Teslafly/Moxie_drive_mini_drv/3dmodels/xt-60-family-1.snapshot.6/xt60 fam1.PNG

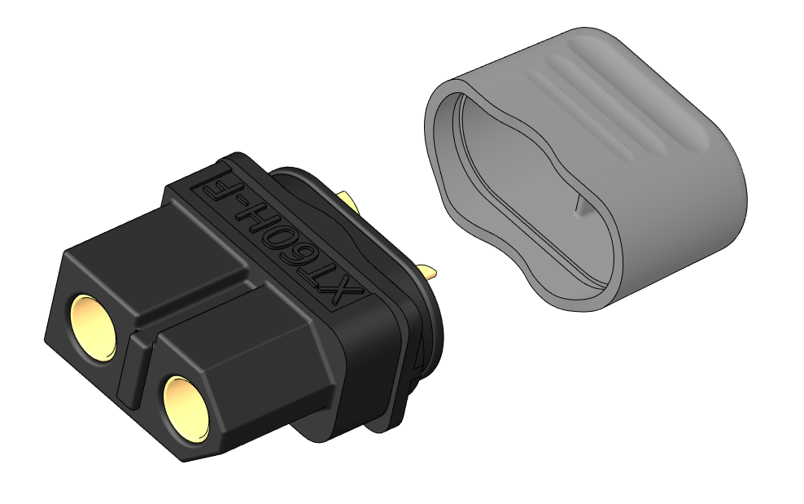
3dmodels/xt-60-family-1.snapshot.6/xt60 fam1.PNG
