Teslafly/Moxie_drive_mini_drv/3dmodels/MachineScrews/Screw_Machine_M3x14.SLDPRT

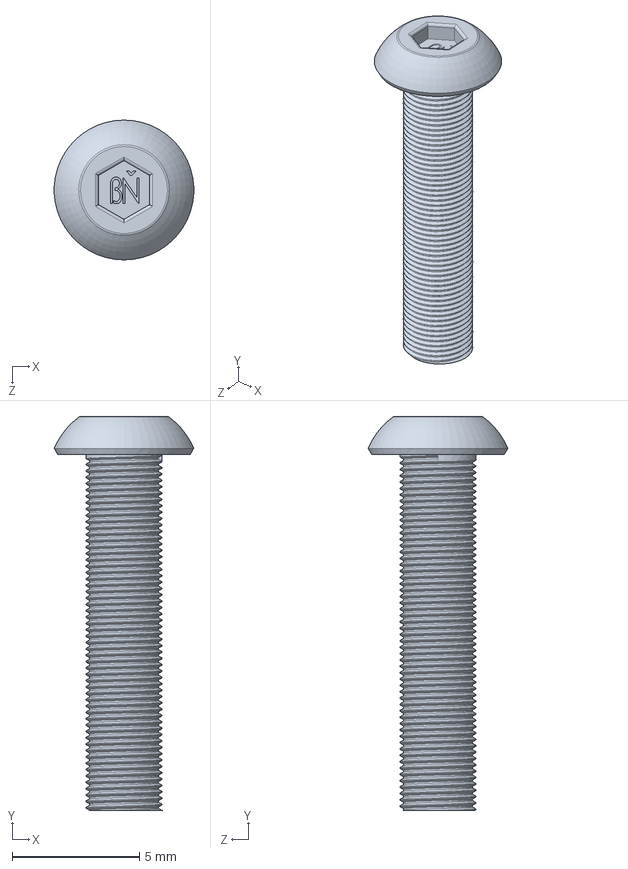
[picture p22: CAD file, 2019-12-04]
3dmodels/MachineScrews/Screw_Machine_M3x14.SLDPRT
5.49 x 15.5 x 5.50 mm
