Teslafly/Moxie_drive_mini_drv/3dmodels/MachineScrews/Nut_Machine_M3x2.SLDPRT

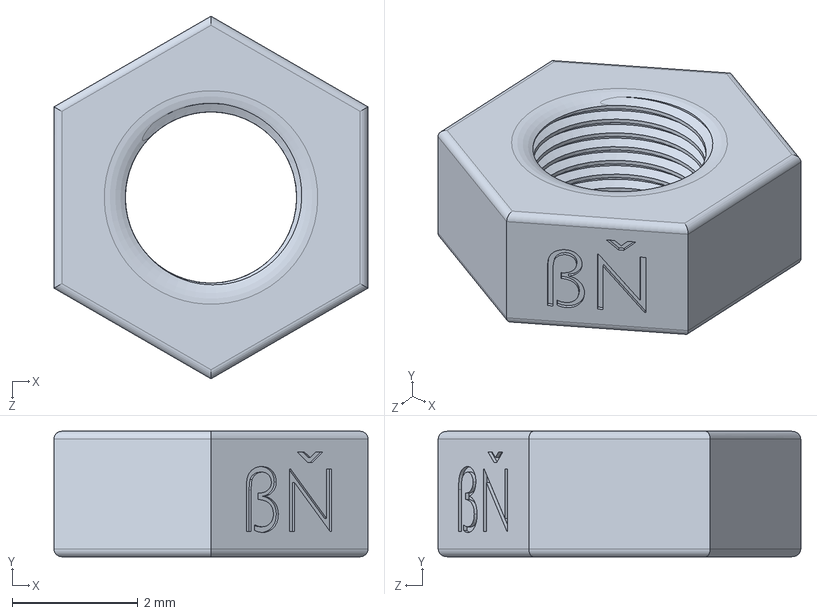
[picture p23: CAD file, 2019-12-04]
3dmodels/MachineScrews/Nut_Machine_M3x2.SLDPRT
5.00 x 2.00 x 5.77 mm
