Teslafly/Moxie_drive_mini_drv/3dmodels/MachineScrews/Screw_Machine_M3x18.SLDPRT

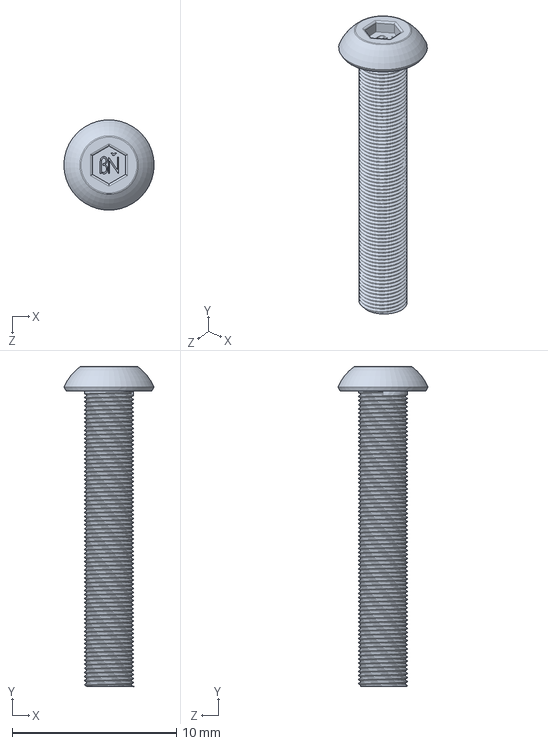
[picture p24: CAD file, 2019-12-04]
3dmodels/MachineScrews/Screw_Machine_M3x18.SLDPRT
5.49 x 19.5 x 5.50 mm
