Teslafly/Moxie_drive_mini_drv/3dmodels/MachineScrews/Screw_Machine_M3x16.SLDPRT

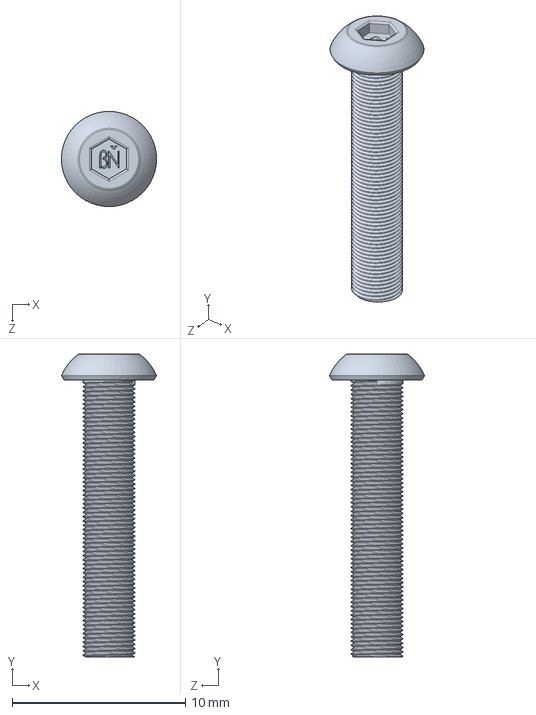
[picture p25: CAD file, 2019-12-04]
3dmodels/MachineScrews/Screw_Machine_M3x16.SLDPRT
5.50 x 17.5 x 5.50 mm
